dac63701/60WKeyboard/review-files/layers/60WKeyboard-In1_Cu.png

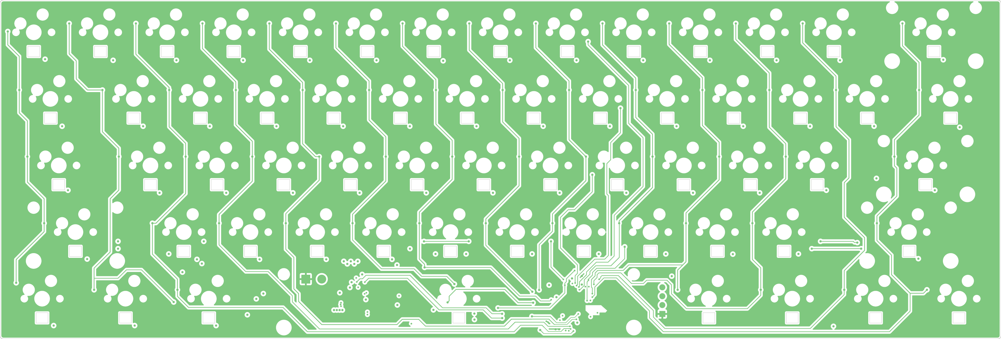
review-files/layers/60WKeyboard-In1_Cu.png
